funvill/London-Underground-PCB/firmware/Londonmap/src/stations.h

// Station names map to LED indices on the strip.
// Keep this header lightweight so it can be reused across projects.
#pragma once

#include <Arduino.h>

using uint16 = uint16_t;

// Use this for stations you haven't assigned to an LED yet.
// (Avoid using 0 as a placeholder, since LED index 0 is valid.)
const uint16 UNMAPPED_LED = 0xFFFF;

const uint16 ABBEY_ROAD = 531;
const uint16 ABBEY_WOOD = 476;
const uint16 ACTON_CENTRAL = 62;
const uint16 ACTON_MAIN_LINE = 60;
const uint16 ACTON_TOWN_A = 13;
const uint16 ACTON_TOWN_B = 64;
const uint16 ACTON_TOWN_C = 65;
const uint16 ADDINGTON_VILLAGE = 443;
const uint16 ADDISCOMBE = 447;
const uint16 ALDGATE = 338;
const uint16 ALDGATE_EAST = 343;
const uint16 ALL_SAINTS = 417;
const uint16 ALPERTON = 100;
const uint16 AMERSHAM = 35;
const uint16 AMPERE_WAY = 297;
const uint16 ANERLEY = 315;
const uint16 ANGEL = 272;
const uint16 ARCHWAY = 372;
const uint16 ARENA = 450;
const uint16 ARNOS_GROVE = 389;
const uint16 ARSENAL = 364;
const uint16 AVENUE_ROAD = 454;
const uint16 BAKER_STREET_A = 140;
const uint16 BAKER_STREET_B = 141;
const uint16 BALHAM = 187;
const uint16 BANK_A = 280;
const uint16 BANK_B = 281;
const uint16 BARBICAN = UNMAPPED_LED;
const uint16 BARKING_A = 505;
const uint16 BARKING_B = 506;
const uint16 BARKING_RIVERSIDE = 507;
const uint16 BARKINGSIDE = 555;
const uint16 BARONS_COURT = 80;
const uint16 BATTERSEA_POWER_STATION = 207;
const uint16 BAYSWATER = 145;
const uint16 BECKENHAM_HILL = 466;
const uint16 BECKENHAM_JUNCTION = 456;
const uint16 BECKENHAM_ROAD = 455;
const uint16 BECKTON = 480;
const uint16 BECKTON_PARK = 483;
const uint16 BECONTREE = 509;
const uint16 BEDDINGTON_LANE = 295;
const uint16 BELGRAVE_WALK = 175;
const uint16 BELLINGHAM = 437;
const uint16 BELSIZE_PARK = 250;
const uint16 BERMONDSEY = 327;
const uint16 BETHNAL_GREEN_CENTRAL_LINE = 346;
const uint16 BETHNAL_GREEN_WEAVER_LINE = 350;
const uint16 BICKLEY = 462;
const uint16 BIRKBECK = 453;
const uint16 BLACKFRIARS = 283;
const uint16 BLACKHORSE_LANE = 448;
const uint16 BLACKHORSE_ROAD_A = 540;
const uint16 BLACKHORSE_ROAD_B = 541;
const uint16 BLACKWALL = 497;
const uint16 BOND_STREET_A = 232;
const uint16 BOND_STREET_B = 233;
const uint16 BOROUGH = 328;
const uint16 BOSTON_MANOR = 10;
const uint16 BOUNDS_GREEN = 388;
const uint16 BOW_CHURCH = 414;
const uint16 BOW_ROAD = UNMAPPED_LED;
const uint16 BRENT_CROSS = 265;
const uint16 BRENT_CROSS_WEST = 256;
const uint16 BRENTWOOD = 519;
const uint16 BRIXTON = 191;
const uint16 BROCKLEY = 320;
const uint16 BROMLEY_BY_BOW = 498;
const uint16 BROMLEY_SOUTH = 463;
const uint16 BRONDESBURY = 131;
const uint16 BRONDESBURY_PARK = 130;
const uint16 BRUCE_GROVE = 402;
const uint16 BUCKHURST_HILL = 564;
const uint16 BURNHAM = 26;
const uint16 BURNT_OAK = 259;
const uint16 BUSH_HILL_PARK = 398;
const uint16 BUSHEY = 116;
const uint16 CALEDONIAN_ROAD = 362;
const uint16 CALEDONIAN_ROAD_BARNSBURY = 361;
const uint16 CAMBRIDGE_HEATH = 351;
const uint16 CAMDEN_ROAD = 271;
const uint16 CAMDEN_TOWN = 248;
const uint16 CANADA_WATER = 325;
const uint16 CANARY_WHARF_A = 421;
const uint16 CANARY_WHARF_B = 422;
const uint16 CANNING_TOWN_A = 494;
const uint16 CANNING_TOWN_B = 495;
const uint16 CANNON_STREET = UNMAPPED_LED;
const uint16 CANONBURY = 356;
const uint16 CANONS_PARK = 119;
const uint16 CARPENDERS_PARK = 115;
const uint16 CARSHALTON = 170;
const uint16 CATFORD = 436;
const uint16 CENTRALE = 301;
const uint16 CHADWELL_HEATH = 523;
const uint16 CHALFONT_LATIMER = 37;
const uint16 CHALK_FARM = 249;
const uint16 CHANCERY_LANE = 277;
const uint16 CHARING_CROSS = 223;
const uint16 CHARLTON = 471;
const uint16 CHESHAM = 36;
const uint16 CHESHUNT = 393;
const uint16 CHIGWELL = 559;
const uint16 CHINGFORD = 542;
const uint16 CHISWICK_PARK = 66;
const uint16 CHORLEYWOOD = 38;
const uint16 CHURCH_STREET = 306;
const uint16 CITY_THAMESLINK = 278;
const uint16 CLAPHAM_COMMON = 189;
const uint16 CLAPHAM_HIGH_STREET = 202;
const uint16 CLAPHAM_JUNCTION_A = 204;
const uint16 CLAPHAM_JUNCTION_B = 205;
const uint16 CLAPHAM_NORTH = 190;
const uint16 CLAPHAM_SOUTH = 188;
const uint16 CLAPTON = 536;
const uint16 COCKFOSTERS = 392;
const uint16 COLINDALE = 258;
const uint16 COLLIERS_WOOD = 180;
const uint16 COOMBE_LANE = 441;
const uint16 COULSDON_SOUTH = 307;
const uint16 COVENT_GARDEN = 276;
const uint16 CRICKLEWOOD = 255;
const uint16 CROFTON_PARK = 435;
const uint16 CROSSHARBOUR = 425;
const uint16 CROUCH_HILL = 368;
const uint16 CROXLEY = 40;
const uint16 CRYSTAL_PALACE = 314;
const uint16 CUSTOM_HOUSE_FOR_EXCEL_A = 486;
const uint16 CUSTOM_HOUSE_FOR_EXCEL_B = 487;
const uint16 CUTTY_SARK_FOR_MARITIME_GREENWICH = 428;
const uint16 CYPRUS = 482;
const uint16 DAGENHAM_EAST = 511;
const uint16 DAGENHAM_HEATHWAY = 510;
const uint16 DALSTON_JUNCTION = 355;
const uint16 DALSTON_KINGSLAND = 359;
const uint16 DARTFORD = 458;
const uint16 DEBDEN = 566;
const uint16 DENMARK_HILL_A = 291;
const uint16 DENMARK_HILL_B = 292;
const uint16 DEPTFORD = 429;
const uint16 DEPTFORD_BRIDGE = 432;
const uint16 DEVONS_ROAD = 415;
const uint16 DOLLIS_HILL = 126;
const uint16 DUNDONALD_ROAD = 182;
const uint16 EALING_BROADWAY = 15;
const uint16 EALING_COMMON = 14;
const uint16 EARLS_COURT_A = 151;
const uint16 EARLS_COURT_B = 152;
const uint16 EAST_ACTON = 87;
const uint16 EAST_CROYDON_A = 311;
const uint16 EAST_CROYDON_B = 312;
const uint16 EAST_FINCHLEY = 374;
const uint16 EAST_HAM = 504;
const uint16 EAST_INDIA = 496;
const uint16 EAST_PUTNEY = 158;
const uint16 EASTCOTE = UNMAPPED_LED;
const uint16 EDGEWARE = 260;
const uint16 EDGEWARE_ROAD_A = 93;
const uint16 EDGEWARE_ROAD_B = 133;
const uint16 EDGEWARE_ROAD_C = 142;
const uint16 EDGEWARE_ROAD_D = 143;
const uint16 EDMONTON_GREEN = 399;
const uint16 ELEPHANT_CASTLE_A = 289;
const uint16 ELEPHANT_CASTLE_B = 290;
const uint16 ELMERS_END = 451;
const uint16 ELM_PARK = 512;
const uint16 ELSTREE_BOREHAMWOOD = 262;
const uint16 ELVERSON_ROAD = 433;
const uint16 EMBANKMENT_A = 221;
const uint16 EMBANKMENT_B = 222;
const uint16 EMERSON_PARK = 517;
const uint16 ENFIELD_TOWN = 397;
const uint16 EPPING = 568;
const uint16 EUSTON_A = 241;
const uint16 EUSTON_B = 242;
const uint16 EUSTON_C = 243;
const uint16 EUSTON_D = 244;
const uint16 EUSTON_SQUARE = UNMAPPED_LED;
const uint16 FAIRLOP = 556;
const uint16 FARRINGDON = UNMAPPED_LED;
const uint16 FIELDWAY = 444;
const uint16 FINCHLEY_CENTRAL = 375;
const uint16 FINCHLEY_ROAD_A = 135;
const uint16 FINCHLEY_ROAD_B = 137;
const uint16 FINCHLEY_ROAD_FROGNAL_A = 136;
const uint16 FINCHLEY_ROAD_FROGNAL_B = 252;
const uint16 FINSBURY_PARK_A = 365;
const uint16 FINSBURY_PARK_B = 366;
const uint16 FOREST_GATE = 528;
const uint16 FOREST_HILL = 318;
const uint16 FULHAM_BROADWAY = 155;
const uint16 GALLIONS_REACH = 481;
const uint16 GANTS_HILL = 553;
const uint16 GEORGE_STREET = 305;
const uint16 GIDEA_PARK = 521;
const uint16 GLOUCESTER_ROAD_A = 211;
const uint16 GLOUCESTER_ROAD_B = 212;
const uint16 GOLDERS_GREEN = 266;
const uint16 GOLDHAWK_ROAD = 83;
const uint16 GOODGE_STREET = 237;
const uint16 GOODMAYES = 524;
const uint16 GOSPEL_OAK_A = 268;
const uint16 GOSPEL_OAK_B = 269;
const uint16 GRANGE_HILL = 558;
const uint16 GRAVEL_HILL = 442;
const uint16 GREAT_PORTLAND_STREET = 240;
const uint16 GREEN_PARK = 226;
const uint16 GREENFORD = 55;
const uint16 GREENWICH_A = 430;
const uint16 GREENWICH_B = 431;
const uint16 GUNNERSBURY_A = 67;
const uint16 GUNNERSBURY_B = 72;
const uint16 HACKBRIDGE = 171;
const uint16 HACKNEY_CENTRAL = 409;
const uint16 HACKNEY_DOWNS_A = 407;
const uint16 HACKNEY_DOWNS_B = 408;
const uint16 HACKNEY_WICK = 411;
const uint16 HAGGERSTON = 354;
const uint16 HAINAULT = 557;
const uint16 HAMMERSMITH_A = 77;
const uint16 HAMMERSMITH_B = 81;
const uint16 HAMMERSMITH_C = 82;
const uint16 HAMPSTEAD = 267;
const uint16 HAMPSTEAD_HEATH = 251;
const uint16 HANGER_LANE = 57;
const uint16 HANWELL = 19;
const uint16 HARLESDEN = 104;
const uint16 HAROLD_WOOD = 520;
const uint16 HARRINGAY_GREEN_LANES = 385;
const uint16 HARRINGTON_ROAD = 452;
const uint16 HARROW_WEALDSTONE = 112;
const uint16 HARROW_ON_THE_HILL = 47;
const uint16 HATCH_END = 114;
const uint16 HATTON_CROSS = 6;
const uint16 HAYDONS_ROAD = 184;
const uint16 HAYES_HARLINGTON = 21;
const uint16 HEADSTONE_LANE = 113;
const uint16 HEATHROW_TERMINALS_2_3_A = 4;
const uint16 HEATHROW_TERMINALS_2_3_B = 5;
const uint16 HEATHROW_TERMINAL_4_A = 0;
const uint16 HEATHROW_TERMINAL_4_B = 1;
const uint16 HEATHROW_TERMINAL_5_A = 2;
const uint16 HEATHROW_TERMINAL_5_B = 3;
const uint16 HENDON = 257;
const uint16 HENDON_CENTRAL = 264;
const uint16 HERNE_HILL = 196;
const uint16 HERON_QUAYS = 423;
const uint16 HIGH_BARNET = 380;
const uint16 HIGH_STREET_KENSINGTON = UNMAPPED_LED;
const uint16 HIGHAMS_PARK = 543;
const uint16 HIGHBURY_ISLINGTON_A = 357;
const uint16 HIGHBURY_ISLINGTON_B = 360;
const uint16 HIGHGATE = 373;
const uint16 HILLINGDON = 32;
const uint16 HOLBORN = 275;
const uint16 HOLLAND_PARK = 146;
const uint16 HOLLOWAY_ROAD = 363;
const uint16 HOMERTON = 410;
const uint16 HONOR_OAK_PARK = 319;
const uint16 HORNCHURCH = 513;
const uint16 HOUNSLOW_CENTRAL = 8;
const uint16 HOUNSLOW_EAST = 9;
const uint16 HOUNSLOW_WEST = 7;
const uint16 HOXTON = 353;
const uint16 HYDE_PARK_CORNER = 227;
const uint16 ICKENHAM = 33;
const uint16 IFS_CLOUD_GREENWICH_PENINSULA = 469;
const uint16 IFS_CLOUD_ROYAL_DOCKS = 492;
const uint16 ILFORD = 526;
const uint16 IMPERIAL_WHARF_ = 206;
const uint16 ISLAND_GARDENS = 427;
const uint16 KENNINGTON_A = 199;
const uint16 KENNINGTON_B = 200;
const uint16 KENSAL_GREEN = 98;
const uint16 KENSAL_RISE = 129;
const uint16 KENSINGTON_OLYMPIA_A = 149;
const uint16 KENSINGTON_OLYMPIA_B = 150;
const uint16 KENTISH_TOWN = 369;
const uint16 KENTISH_TOWN_WEST = 270;
const uint16 KENTON = 111;
const uint16 KEW_GARDENS_A = 68;
const uint16 KEW_GARDENS_B = 71;
const uint16 KILBURN = 128;
const uint16 KILBURN_HIGH_ROAD = 132;
const uint16 KILBURN_PARK = 96;
const uint16 KING_GEORGE_V = 488;
const uint16 KING_HENRYS_DRIVE = 445;
const uint16 KINGS_CROSS_ST_PANCRAS_A = 245;
const uint16 KINGS_CROSS_ST_PANCRAS_B = 246;
const uint16 KINGSBURY = 122;
const uint16 KNIGHTSBRIDGE = 228;
const uint16 LADBROKE_GROVE = 90;
const uint16 LAMBETH_NORTH = 288;
const uint16 LANCASTER_GATE = 230;
const uint16 LANGDON_PARK = 416;
const uint16 LANGLEY = 23;
const uint16 LATIMER_ROAD = 89;
const uint16 LEBANON_ROAD = 438;
const uint16 LEICESTER_SQUARE = 224;
const uint16 LEWISHAM = 434;
const uint16 LEYTON = 534;
const uint16 LEYTON_MIDLAND_ROAD = 548;
const uint16 LEYTONSTONE = 550;
const uint16 LEYTONSTONE_HIGH_ROAD = 549;
const uint16 LIMEHOUSE = 335;
const uint16 LIVERPOOL_STREET_A = 342;
const uint16 LIVERPOOL_STREET_B = 343;
const uint16 LLOYD_PARK = 440;
const uint16 LONDON_BRIDGE_A = 329;
const uint16 LONDON_BRIDGE_B = 330;
const uint16 LONDON_CITY_AIRPORT = 489;
const uint16 LONDON_FIELDS = 352;
const uint16 LOUGHBOROUGH_JUNCTION = 197;
const uint16 LOUGHTON = 565;
const uint16 MAIDA_VALE = 95;
const uint16 MANOR_HOUSE = 367;
const uint16 MANOR_PARK = 527;
const uint16 MANSION_HOUSE = 282;
const uint16 MARBLE_ARCH = 231;
const uint16 MARYLAND = 533;
const uint16 MARYLEBONE = 134;
const uint16 MAZE_HILL = 467;
const uint16 MERTON_PARK = 181;
const uint16 MILE_END = 348;
const uint16 MILL_HILL_BROADWAY = 261;
const uint16 MILL_HILL_EAST = 376;
const uint16 MITCHAM = 174;
const uint16 MITCHAM_EASTFIELDS = 193;
const uint16 MITCHAM_JUNCTION_A = 172;
const uint16 MITCHAM_JUNCTION_B = 173;
const uint16 MONUMENT = UNMAPPED_LED;
const uint16 MOOR_PARK = 42;
const uint16 MOORGATE = 339;
const uint16 MORDEN = 178;
const uint16 MORDEN_ROAD = 177;
const uint16 MORDEN_SOUTH = 165;
const uint16 MORNINGTON_CRESCENT = 247;
const uint16 MUDCHUTE = 426;
const uint16 NEASDEN = 125;
const uint16 NEW_ADDINGTON = 446;
const uint16 NEW_BARNET = UNMAPPED_LED;
const uint16 NEW_CROSS = 233;
const uint16 NEW_CROSS_GATE = 322;
const uint16 NEW_SOUTHGATE = 384;
const uint16 NEWBURY_PARK = 554;
const uint16 NINE_ELMS = 208;
const uint16 NORTH_ACTON = 88;
const uint16 NORTH_EALING = 59;
const uint16 NORTH_GREENWICH = 468;
const uint16 NORTH_HARROW = 46;
const uint16 NORTH_WEMBLEY = 107;
const uint16 NORTHFIELDS = 11;
const uint16 NORTHOLT = 54;
const uint16 NORTHWICK_PARK = 109;
const uint16 NORTHWOOD = 43;
const uint16 NORTHWOOD_HILLS = 44;
const uint16 NORTHWOOD_JUNCTION = 313;
const uint16 NOTTING_HILL_GATE = 230;
const uint16 NUNHEAD = 321;
const uint16 OAKLEIGH_PARK = 381;
const uint16 OAKWOOD = 391;
const uint16 OLD_STREET = 340;
const uint16 ORPINGTON_ = 457;
const uint16 OSTERLEY = 9;
const uint16 OVAL = 198;
const uint16 OXFORD_CIRCUS = 234;
const uint16 PADDINGTON = 144;
const uint16 PARK_ROYAL = 58;
const uint16 PARSONS_GREEN = 156;
const uint16 PECKHAM_RYE = 293;
const uint16 PENGE_WEST = 316;
const uint16 PERIVALE = 56;
const uint16 PETTS_WOOD = 461;
const uint16 PHIPPS_BRIDGE = 176;
const uint16 PICCADILLY_CIRCUS = 225;
const uint16 PIMLICO = 210;
const uint16 PINNER = 45;
const uint16 PLAISTOW = 502;
const uint16 PLUMSTEAD_ = 475;
const uint16 PONTOON_DOCK = 490;
const uint16 POPLAR = 418;
const uint16 PRESTON_ROAD = 110;
const uint16 PRINCE_REGENT = 485;
const uint16 PUDDING_MILL_LANE = 413;
const uint16 PURLEY = 309;
const uint16 PUTNEY_BRIDGE = 157;
const uint16 QUEENS_PARK = 97;
const uint16 QUEENS_ROAD_PECKHAM = 294;
const uint16 QUEENSBURY = 121;
const uint16 QUEENSWAY = 229;
const uint16 RAVENSBOURNE = 465;
const uint16 RAVENSCOURT_PARK = 76;
const uint16 RAYNERS_LANE = 49;
const uint16 READING = 30;
const uint16 RECTORY_ROAD = 406;
const uint16 REDBRIDGE = 552;
const uint16 REEVES_CORNER = 300;
const uint16 REGENTS_PARK = 239;
const uint16 RICHMOND_A = 69;
const uint16 RICHMOND_B = 70;
const uint16 RICKMANSWORTH = 41;
const uint16 RODING_VALLEY = 560;
const uint16 ROMFORD = 522;
const uint16 ROTHERHITHE = 326;
const uint16 ROYAL_ALBERT = 484;
const uint16 ROYAL_OAK = 92;
const uint16 ROYAL_VICTORIA = 493;
const uint16 RUISLIP = 51;
const uint16 RUISLIP_GARDENS = 52;
const uint16 RUISLIP_MANOR = 50;
const uint16 RUSSELL_SQUARE_A = 273;
const uint16 RUSSELL_SQUARE_B = 274;
const uint16 ST_HELIER = 166;
const uint16 ST_JAMES_STREET = 537;
const uint16 ST_JAMESS_PARK = 218;
const uint16 ST_JOHNS_WOOD = 139;
const uint16 ST_MARY_CRAY = 460;
const uint16 ST_PAULS = 279;
const uint16 SANDILANDS = 439;
const uint16 SEVEN_KINGS = 525;
const uint16 SEVEN_SISTERS = 403;
const uint16 SHADWELL_A = 334;
const uint16 SHADWELL_B = 337;
const uint16 SHENFIELD = 518;
const uint16 SHEPHERDS_BUSH_A = 147;
const uint16 SHEPHERDS_BUSH_B = 148;
const uint16 SHEPHERDS_BUSH_MARKET = 84;
const uint16 SHOREDITCH_HIGH_STREET = 349;
const uint16 SHORTLANDS = 464;
const uint16 SILVER_STREET = 400;
const uint16 SLADE_GREEN_ = 477;
const uint16 SLOANE_SQUARE = 215;
const uint16 SLOUGH = 25;
const uint16 SNARESBROOK = 561;
const uint16 SOUTH_ACTON = 63;
const uint16 WEST_CROYDON_A = 302;
const uint16 WEST_CROYDON_B = 303;
const uint16 SOUTH_CROYDON = 310;
const uint16 SOUTH_EALING = 12;
const uint16 SOUTH_HAMPSTEAD = UNMAPPED_LED;
const uint16 SOUTH_HARROW = 103;
const uint16 SOUTH_KENSINGTON_A = 213;
const uint16 SOUTH_KENSINGTON_B = 214;
const uint16 SOUTH_KENTON = 108;
const uint16 SOUTH_MERTON = 164;
const uint16 SOUTH_QUAY = 424;
const uint16 SOUTH_RUISLIP = 53;
const uint16 SOUTH_TOTTENHAM = 539;
const uint16 SOUTH_WIMBLEDON = 179;
const uint16 SOUTH_WOODFORD = 562;
const uint16 SOUTHALL = 20;
const uint16 SOUTHBURY = 396;
const uint16 SOUTHFIELDS = 159;
const uint16 SOUTHGATE = 390;
const uint16 SOUTHWARK = 286;
const uint16 STAMFORD_BROOK = 75;
const uint16 STAMFORD_HILL = 404;
const uint16 STANMORE = 120;
const uint16 STAR_LANE = 501;
const uint16 STEPNEY_GREEN = 347;
const uint16 STOCKWELL = 201;
const uint16 STOKE_NEWINGTON = 405;
const uint16 STONEBRIDGE_PARK = 105;
const uint16 STRATFORD = 412;
const uint16 STRATFORD_HIGH_STREET = 532;
const uint16 STRATFORD_INTERNATIONAL = 535;
const uint16 STREATHAM = 194;
const uint16 SUDBURY_HILL = 102;
const uint16 SUDBURY_TOWN = 101;
const uint16 SURREY_QUAYS = 324;
const uint16 SUTTON_ = 169;
const uint16 SUTTON_COMMON = 167;
const uint16 SWANLEY_ = 479;
const uint16 SWISS_COTTAGE = 138;
const uint16 SYDENHAM = 317;
const uint16 TAPLOW = 27;
const uint16 TEMPLE = 284;
const uint16 THEOBALDS_GROVE = 394;
const uint16 THERAPIA_LANE = 296;
const uint16 THEYDON_BOIS = 567;
const uint16 TOOTING = 192;
const uint16 TOOTING_BEC = 186;
const uint16 TOOTING_BROADWAY = 185;
const uint16 TOTTENHAM_COURT_ROAD_A = 235;
const uint16 TOTTENHAM_COURT_ROAD_B = 236;
const uint16 TOTTENHAM_HALE = 538;
const uint16 TOTTERIDGE_WHETSTONE = 379;
const uint16 TOWER_GATEWAY = 332;
const uint16 TOWER_HILL = 331;
const uint16 TUFNELL_PARK = 370;
const uint16 TULSE_HILL = 195;
const uint16 TURKEY_STREET = 395;
const uint16 TURNHAM_GREEN_A = 73;
const uint16 TURNHAM_GREEN_B = 74;
const uint16 TURNPIKE_LANE = 386;
const uint16 TWYFORD = 29;
const uint16 UPMINSTER_A = 515;
const uint16 UPMINSTER_B = 516;
const uint16 UPMINSTER_BRIDGE = 514;
const uint16 UPNEY = 508;
const uint16 UPPER_HOLLOWAY = 371;
const uint16 UPTON_PARK = 503;
const uint16 UXBRIDGE = 31;
const uint16 VAUXHALL = 209;
const uint16 VICTORIA_A = 216;
const uint16 VICTORIA_B = 217;
const uint16 WADDON_MARSH = 298;
const uint16 WALTHAMSTOW_CENTRAL_A = 545;
const uint16 WALTHAMSTOW_CENTRAL_B = 546;
const uint16 WALTHAMSTOW_QUEENS_ROAD = 547;
const uint16 WANDLE_PARK = 299;
const uint16 WANDSWORTH_ROAD = 203;
const uint16 WANSTEAD = 551;
const uint16 WANSTEAD_PARK = 529;
const uint16 WAPPING = 333;
const uint16 WARREN_STREET = 238;
const uint16 WARWICK_AVENUE = 94;
const uint16 WATERLOO_A = UNMAPPED_LED;
const uint16 WATERLOO_B = UNMAPPED_LED;
const uint16 WATFORD = 39;
const uint16 WATFORD_HIGH_STREET = 117;
const uint16 WATFORD_JUNCTION = 118;
const uint16 WELLESLEY_ROAD = 304;
const uint16 WEMBLEY_CENTRAL = 106;
const uint16 WEMBLEY_PARK = 123;
const uint16 WEST_ACTON = 61;
const uint16 WEST_BROMPTON_A = 153;
const uint16 WEST_BROMPTON_B = 154;
const uint16 WEST_DRAYTON = 22;
const uint16 WEST_EALING = 18;
const uint16 WEST_FINCHLEY = 377;
const uint16 WEST_HAM_A = 499;
const uint16 WEST_HAM_B = 500;
const uint16 WEST_HAMPSTEAD = 253;
const uint16 WEST_HAMPSTEAD_THAMESLINK = 254;
const uint16 WEST_HARROW = 48;
const uint16 WEST_INDIA_QUAY_A = 419;
const uint16 WEST_INDIA_QUAY_B = 420;
const uint16 WEST_KENSINGTON = 79;
const uint16 WEST_RUISLIP = 34;
const uint16 WEST_SILVERTOWN = 491;
const uint16 WEST_SUTTON = 168;
const uint16 WESTBOURNE_PARK = 91;
const uint16 WESTCOMBE_PARK = 470;
const uint16 WESTFERRY = 336;
const uint16 WESTMINSTER_A = 219;
const uint16 WESTMINSTER_B = 220;
const uint16 WHITE_CITY = 86;
const uint16 WHITE_HART_LANE = 401;
const uint16 WHITECHAPEL_A = 344;
const uint16 WHITECHAPEL_B = 345;
const uint16 WILLESDEN_GREEN = 127;
const uint16 WILLESDEN_JUNCTION = 99;
const uint16 WIMBLEDON_A = 161;
const uint16 WIMBLEDON_B = 183;
const uint16 WIMBLEDON_CHASE = 163;
const uint16 WIMBLEDON_PARK_A = 160;
const uint16 WIMBLEDON_PARK_B = 162;
const uint16 WIMBLEDON_PARK_C = 183;
const uint16 WOOD_GREEN = 387;
const uint16 WOOD_LANE = 85;
const uint16 WOOD_STREET = 544;
const uint16 WOODFORD = 563;
const uint16 WOODGRANGE_PARK = 530;
const uint16 WOODSIDE = 449;
const uint16 WOODSIDE_PARK = 378;
const uint16 WOOLWICH = 474;
const uint16 WOOLWICH_ARSENAL_A = 472;
const uint16 WOOLWICH_ARSENAL_B = 473;
